TingliangZhang/Misaka-PCB-v2/KiCAD Lib/SparkFun-KiCad-Libraries/Documentation/Graphics Work/Symbols_raw.png

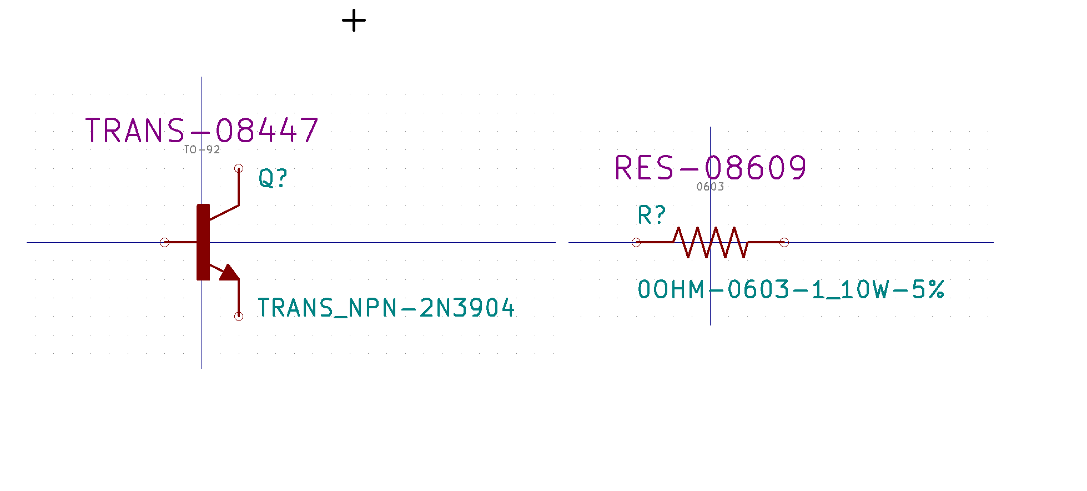
KiCAD Lib/SparkFun-KiCad-Libraries/Documentation/Graphics Work/Symbols_raw.png
