TingliangZhang/Misaka-PCB-v2/KiCAD Lib/SparkFun-KiCad-Libraries/Tools/SparkFun-Eagle-Libraries_Conversion/description_tag_example.jpg

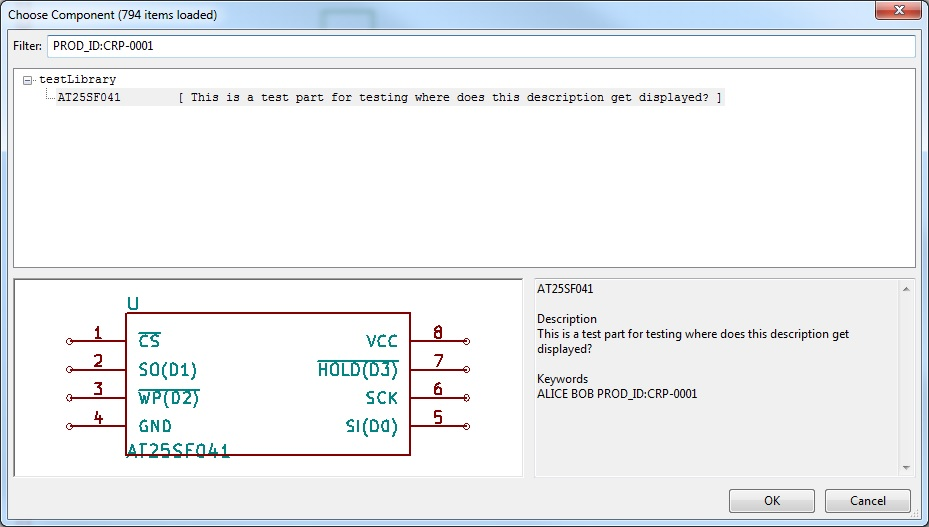
KiCAD Lib/SparkFun-KiCad-Libraries/Tools/SparkFun-Eagle-Libraries_Conversion/description_tag_example.jpg
