TingliangZhang/Misaka-PCB-v2/KiCAD Lib/SparkFun-KiCad-Libraries/Tools/SparkFun-Eagle-Libraries_Conversion/example1.jpg

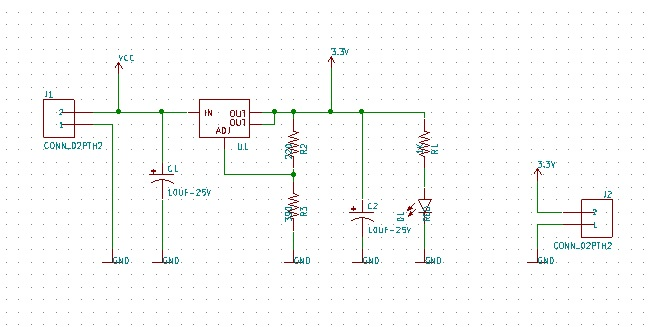
KiCAD Lib/SparkFun-KiCad-Libraries/Tools/SparkFun-Eagle-Libraries_Conversion/example1.jpg
