TingliangZhang/Misaka-PCB-v2/Misaka/Misaka-2.png

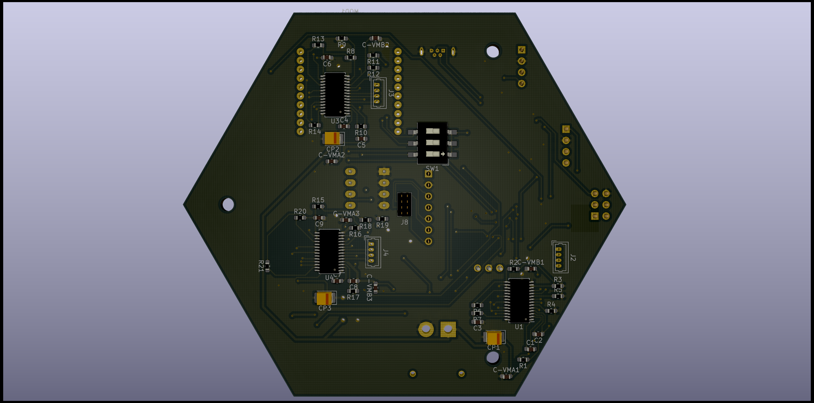
Misaka/Misaka-2.png
