TingliangZhang/Misaka-PCB-v2/Misaka/Misaka-3.png

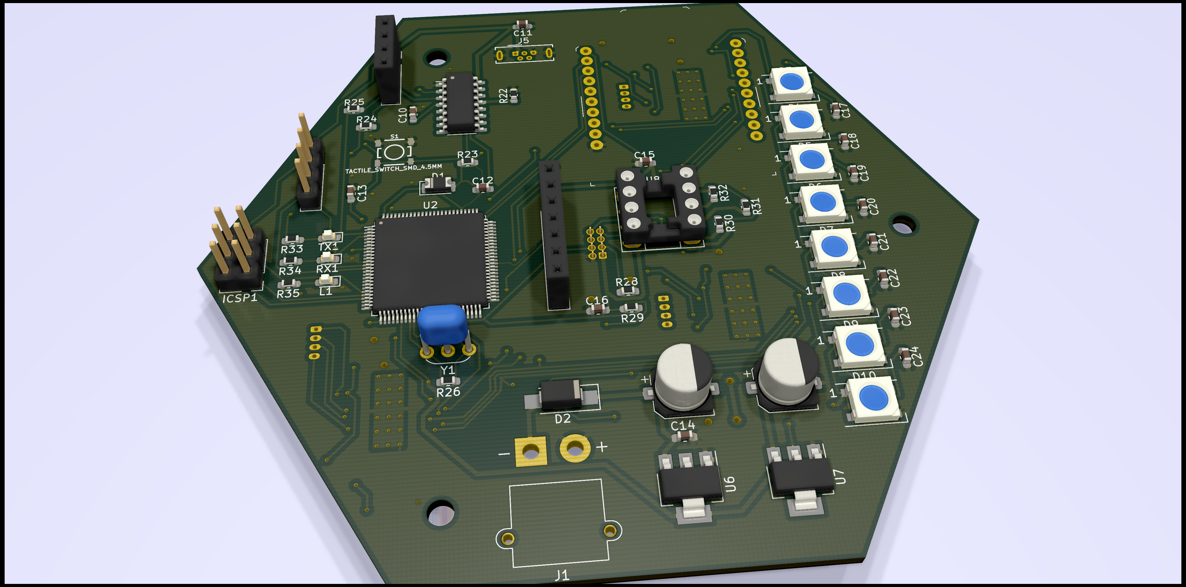
Misaka/Misaka-3.png
