TingliangZhang/Misaka-PCB-v2/Misaka/Misaka.png

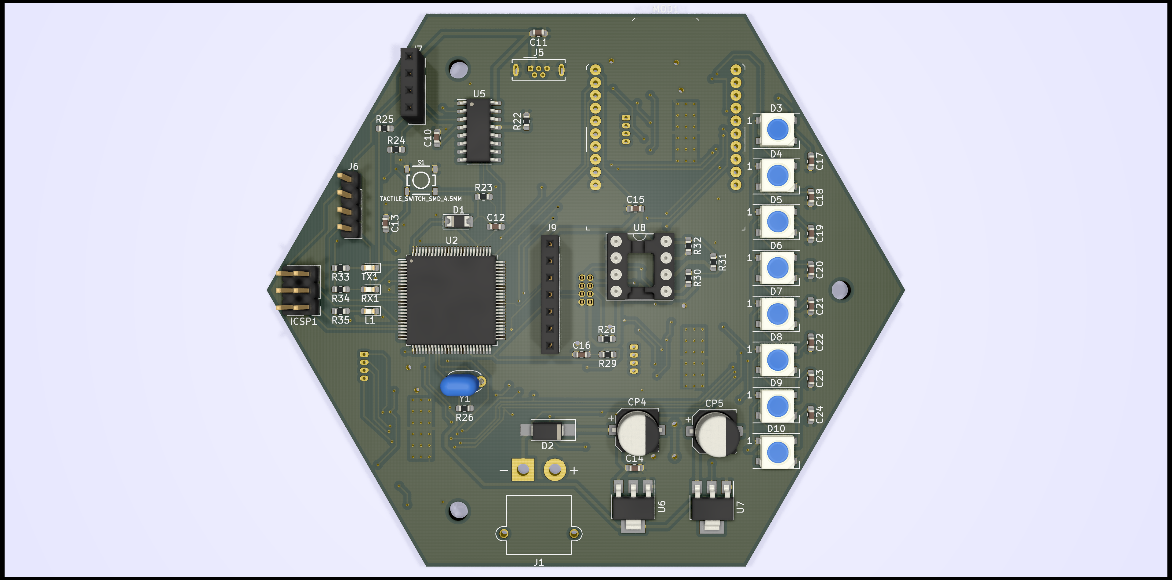
Misaka/Misaka.png
