TingliangZhang/Misaka-PCB-v2/References/MEGA-PRO-CH340GATmega2560/mega-pro-ch340gatmega2560no-pinheaders-3.jpg

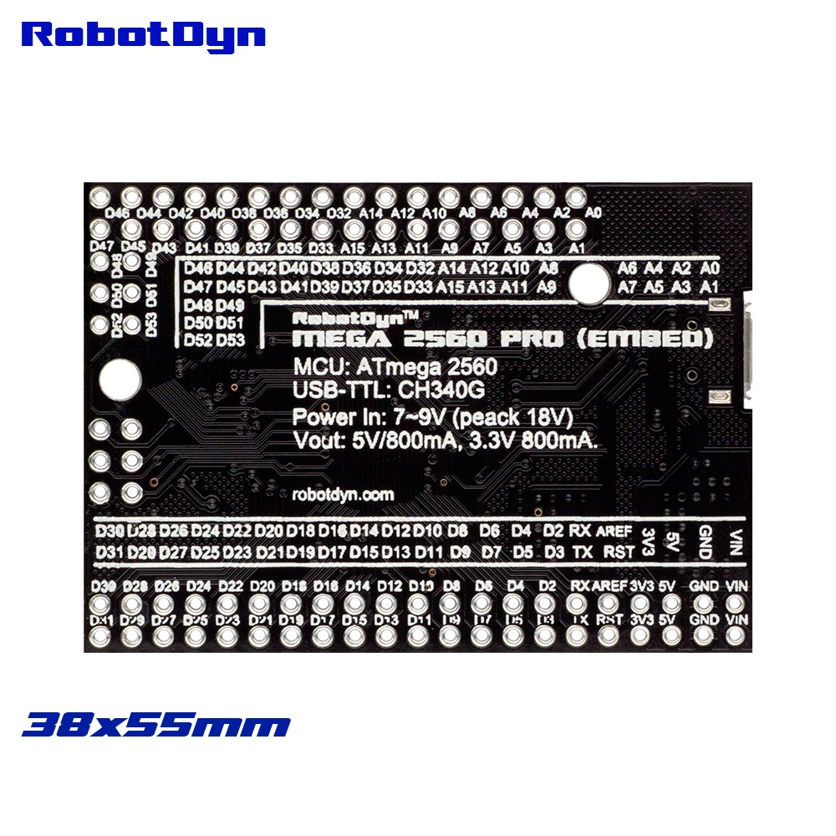
References/MEGA-PRO-CH340GATmega2560/mega-pro-ch340gatmega2560no-pinheaders-3.jpg
