TingliangZhang/Misaka-PCB-v2/KiCAD Lib/SparkFun-KiCad-Libraries/Documentation/Pictures/SymbolGuidelines.png

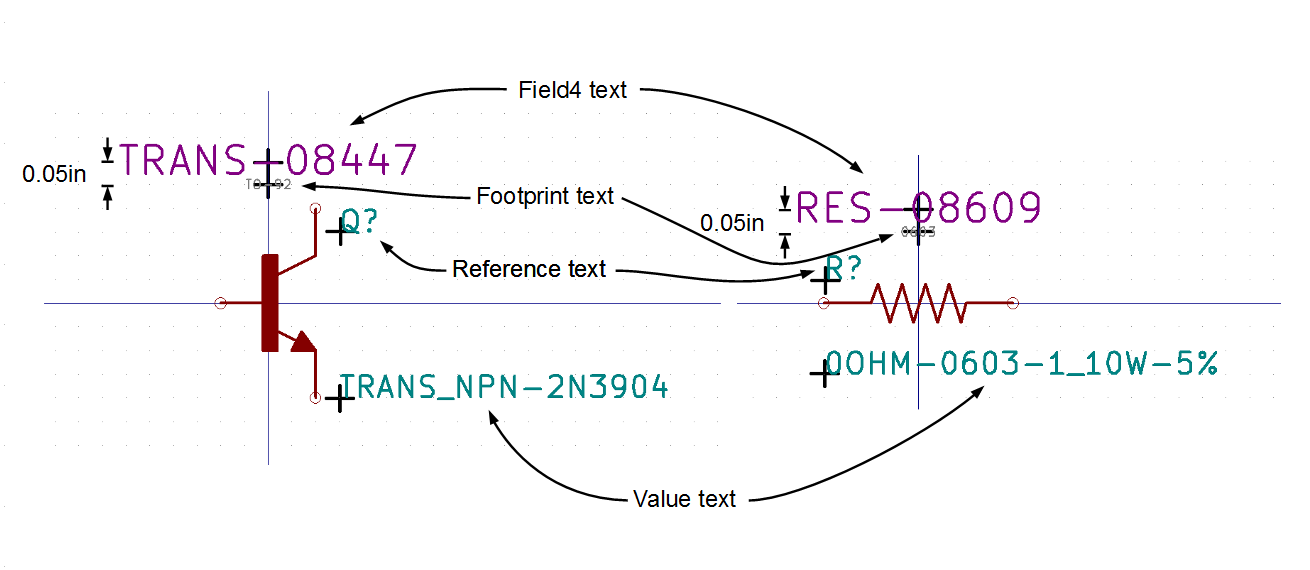
KiCAD Lib/SparkFun-KiCad-Libraries/Documentation/Pictures/SymbolGuidelines.png
